sparkfun/SparkFun_u-blox_NEO-F10N/docs/assets/3d_model/SparkFun_NEO-F10N_3D_image.png

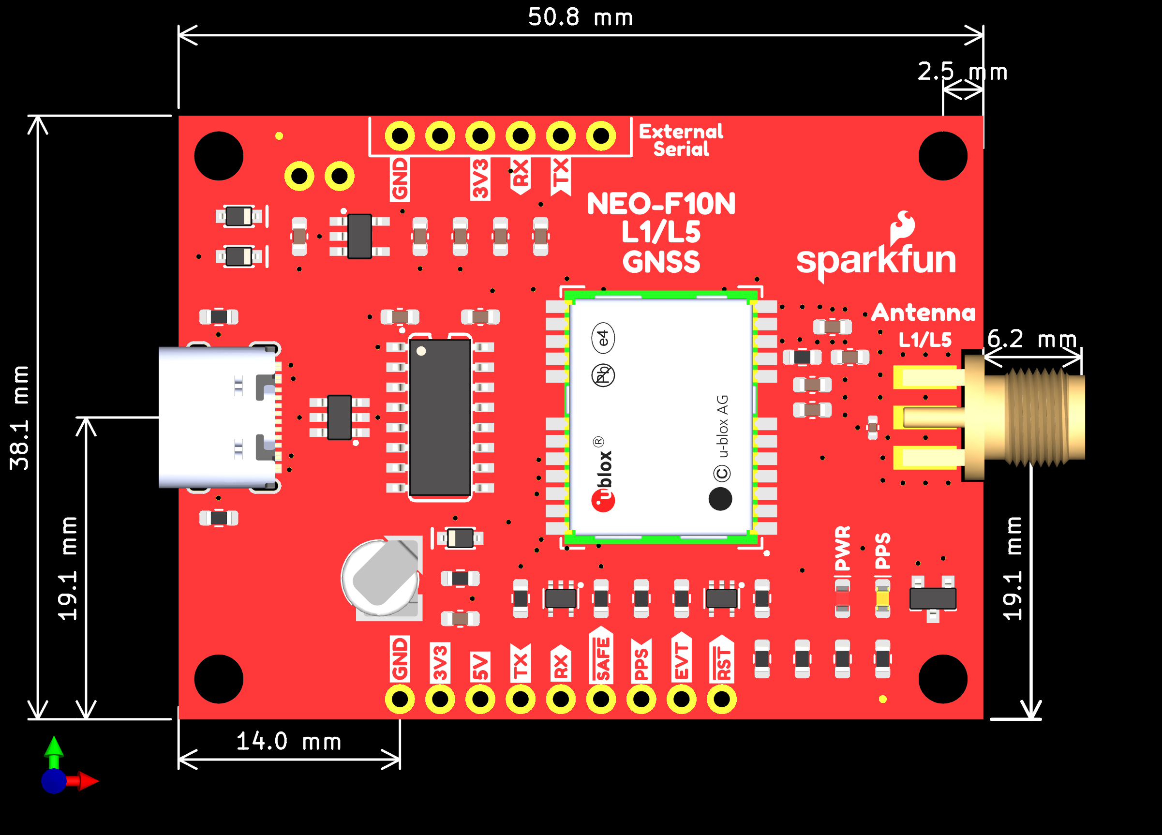
docs/assets/3d_model/SparkFun_NEO-F10N_3D_image.png
