sparkfun/SparkFun_u-blox_NEO-F10N/docs/assets/img/Arduino_NEO-F10N_IoT_RedBoard_ESP32_Output_Satellites.JPG

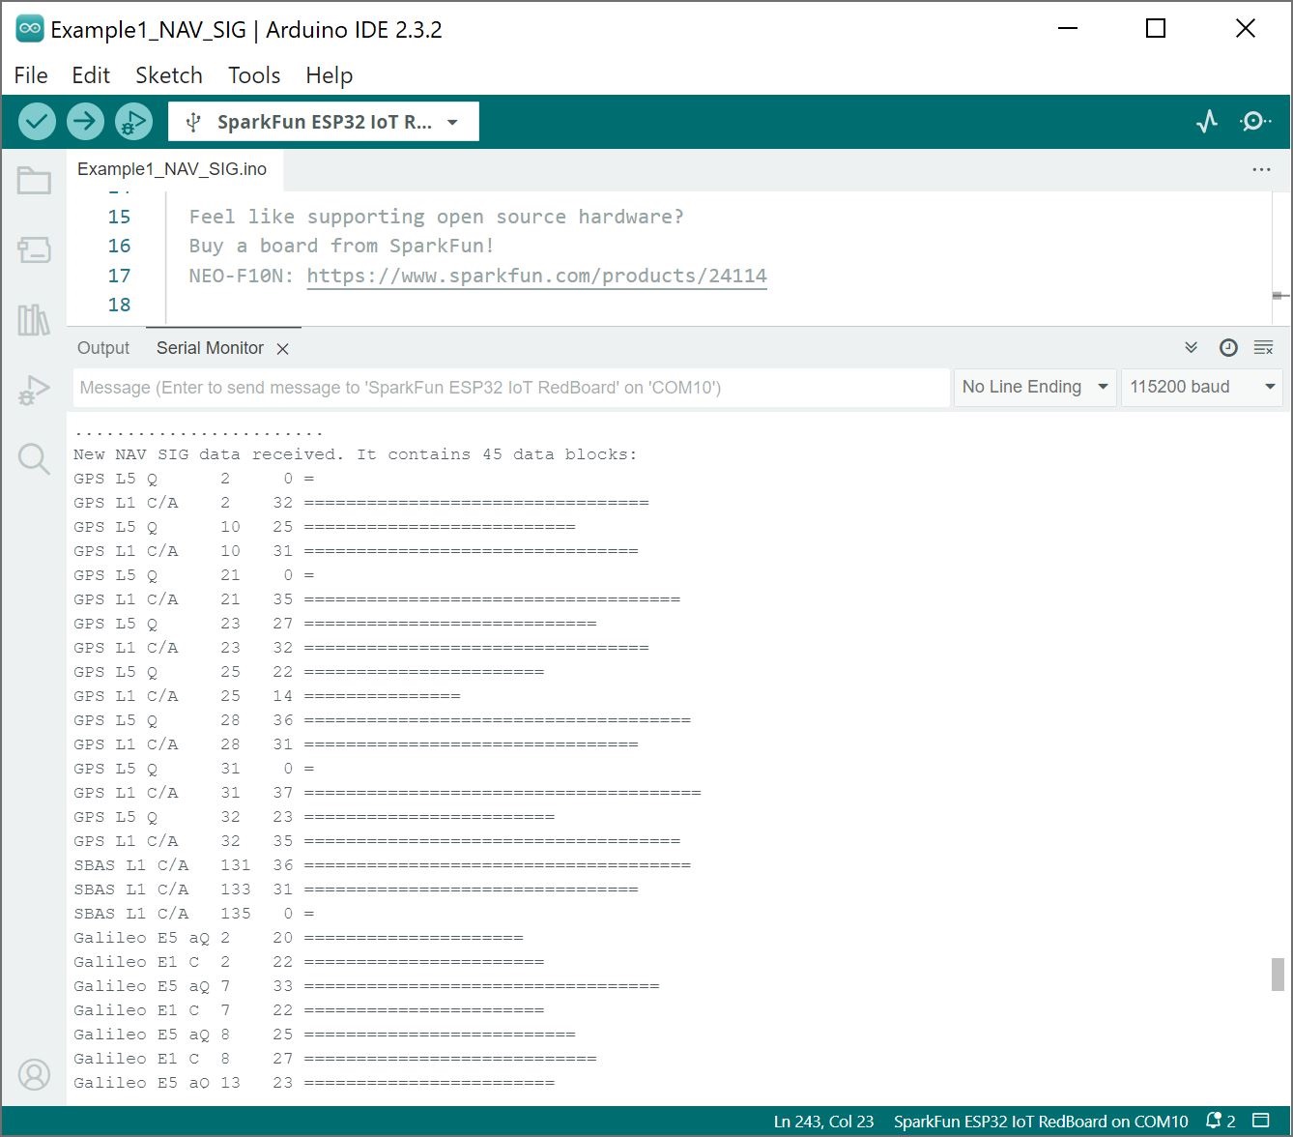
docs/assets/img/Arduino_NEO-F10N_IoT_RedBoard_ESP32_Output_Satellites.JPG
