sparkfun/SparkFun_u-blox_NEO-F10N/docs/assets/img/u-blox_Save_Configuration.JPG

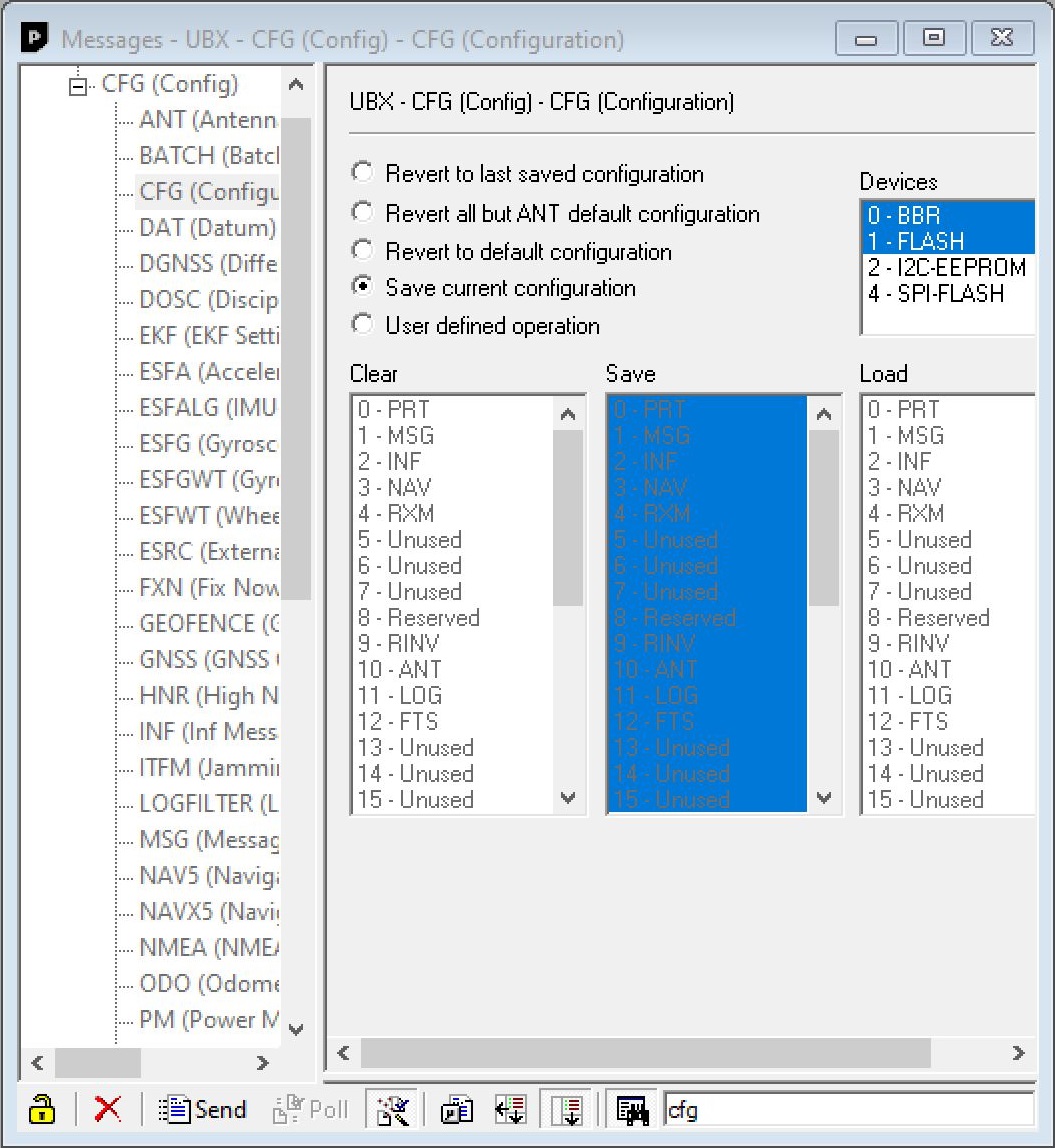
docs/assets/img/u-blox_Save_Configuration.JPG
